mengstr/MCC8/Firmware/MCC8.X/oled.c

#include <stdlib.h>
#include <stdint.h>
#include <string.h>

#include <xc.h>
#include "config.h"
#include "spi.h"
#include "oled.h"


static uint8_t buffer[SSD1306_LCDHEIGHT * SSD1306_LCDWIDTH / 8] = {
0x00, 0x00, 0x00, 0x00, 0x00, 0x00, 0x00, 0x00, 0x00, 0x00, 0x00, 0x00, 0x00, 0x00, 0x00, 0x00,
0x00, 0x00, 0x00, 0x00, 0x00, 0x00, 0x00, 0x00, 0x00, 0x00, 0x00, 0x00, 0x00, 0x00, 0x00, 0x00,
0x00, 0x00, 0x00, 0x00, 0x00, 0x00, 0x00, 0x00, 0x00, 0x00, 0x00, 0x00, 0x00, 0x00, 0x00, 0x00,
0x00, 0x00, 0x00, 0x00, 0x00, 0x00, 0x00, 0x00, 0x00, 0x00, 0x00, 0x00, 0x00, 0x00, 0x00, 0x80,
0x80, 0x80, 0x00, 0x00, 0x00, 0x00, 0x00, 0x00, 0x00, 0x00, 0x00, 0x00, 0x00, 0x00, 0x00, 0x00,
0x00, 0x80, 0x80, 0xC0, 0xC0, 0x00, 0x00, 0x00, 0x00, 0x00, 0x00, 0x00, 0x00, 0x00, 0x00, 0x00,
0x00, 0x00, 0x00, 0x00, 0x00, 0x00, 0x00, 0x00, 0x00, 0x00, 0x00, 0x00, 0x00, 0x00, 0x00, 0x00,
0x00, 0x00, 0x00, 0x00, 0x00, 0x00, 0x00, 0x00, 0x00, 0x00, 0x00, 0x00, 0x00, 0x00, 0x00, 0x00,
0x00, 0x00, 0x00, 0x00, 0x00, 0x00, 0x00, 0x00, 0x00, 0x00, 0x00, 0x00, 0x00, 0x00, 0x00, 0x00,
0x00, 0x00, 0x00, 0x00, 0x80, 0xC0, 0xE0, 0xF0, 0xF8, 0xFC, 0xF8, 0xE0, 0x00, 0x00, 0x00, 0x00,
0x00, 0x00, 0x00, 0x00, 0x00, 0x00, 0x00, 0x00, 0x00, 0x00, 0x00, 0x00, 0x00, 0x80, 0x80, 0x80,
0x80, 0x80, 0x00, 0x80, 0x80, 0x00, 0x00, 0x00, 0x00, 0x80, 0x80, 0x80, 0x80, 0x80, 0x00, 0xFF,
0xFF, 0xFF, 0x00, 0x00, 0x00, 0x00, 0x80, 0x80, 0x80, 0x80, 0x00, 0x00, 0x80, 0x80, 0x00, 0x00,
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
    ,{0x7f, 0x49, 0x49, 0x49, 0x36} // 42 B
    ,{0x3e, 0x41, 0x41, 0x41, 0x22} // 43 C
    ,{0x7f, 0x41, 0x41, 0x22, 0x1c} // 44 D
    ,{0x7f, 0x49, 0x49, 0x49, 0x41} // 45 E
    ,{0x7f, 0x09, 0x09, 0x09, 0x01} // 46 F
    ,{0x3e, 0x41, 0x49, 0x49, 0x7a} // 47 G
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
};



#define SSD1306_CMD_COL_ADD_SET_LSB(column)         (0x00 | (column))
#define SSD1306_CMD_COL_ADD_SET_MSB(column)         (0x10 | (column))
#define SSD1306_CMD_SET_MEMORY_ADDRESSING_MODE      0x20
#define SSD1306_CMD_SET_COLUMN_ADDRESS              0x21
#define SSD1306_CMD_SET_PAGE_ADDRESS                0x22
#define SSD1306_CMD_SET_DISPLAY_START_LINE(line)    (0x40 | (line))
#define SSD1306_CMD_SET_CONTRAST_CONTROL_FOR_BANK0  0x81
#define SSD1306_CMD_SET_CHARGE_PUMP_SETTING         0x8D
#define SSD1306_CMD_SET_SEGMENT_RE_MAP_COL0_SEG0    0xA0
#define SSD1306_CMD_SET_SEGMENT_RE_MAP_COL127_SEG0  0xA1
#define SSD1306_CMD_ENTIRE_DISPLAY_AND_GDDRAM_ON    0xA4
#define SSD1306_CMD_ENTIRE_DISPLAY_ON               0xA5
#define SSD1306_CMD_SET_NORMAL_DISPLAY              0xA6
#define SSD1306_CMD_SET_INVERSE_DISPLAY             0xA7
#define SSD1306_CMD_SET_MULTIPLEX_RATIO             0xA8
#define SSD1306_CMD_SET_DISPLAY_ON                  0xAF
#define SSD1306_CMD_SET_DISPLAY_OFF                 0xAE
#define SSD1306_CMD_SET_PAGE_START_ADDRESS(page)    (0xB0 | (page))
#define SSD1306_CMD_SET_COM_OUTPUT_SCAN_UP          0xC0
#define SSD1306_CMD_SET_COM_OUTPUT_SCAN_DOWN        0xC8
#define SSD1306_CMD_SET_DISPLAY_OFFSET              0xD3
#define SSD1306_CMD_SET_DISPLAY_CLOCK_DIVIDE_RATIO  0xD5
#define SSD1306_CMD_SET_PRE_CHARGE_PERIOD           0xD9
#define SSD1306_CMD_SET_COM_PINS                    0xDA
#define SSD1306_CMD_SET_VCOMH_DESELECT_LEVEL        0xDB
#define SSD1306_CMD_NOP                             0xE3
#define SSD1306_CMD_SCROLL_H_RIGHT                  0x26
#define SSD1306_CMD_SCROLL_H_LEFT                   0x27
#define SSD1306_CMD_CONTINUOUS_SCROLL_V_AND_H_RIGHT 0x29
#define SSD1306_CMD_CONTINUOUS_SCROLL_V_AND_H_LEFT  0x2A
#define SSD1306_CMD_DEACTIVATE_SCROLL               0x2E
#define SSD1306_CMD_ACTIVATE_SCROLL                 0x2F
#define SSD1306_CMD_SET_VERTICAL_SCROLL_AREA        0xA3



//
//
//
void ssd1306_command(uint8_t c) {
    OLED_CS = 1;  // OLED-CS HIGH //digitalWrite(cs, HIGH); *csport |= cspinmask;
    OLED_DC = 0;  // OLED-DC LOW  //digitalWrite(dc, LOW);  *dcport &= ~dcpinmask;
    OLED_CS = 0;  // OLED-CS LOW  //digitalWrite(cs, LOW);  *csport &= ~cspinmask;
    SPI1Write(c);
    OLED_CS = 1;  // OLED-CS HIGH //digitalWrite(cs, HIGH); *csport |= cspinmask;
}


//
//
//
void ssd1306_data(uint8_t c) {
    OLED_CS = 1;  // OLED-CS HIGH //digitalWrite(cs, HIGH); *csport |= cspinmask;
    OLED_DC = 1;  // OLED-DC HIGH  //digitalWrite(dc, LOW);  *dcport &= ~dcpinmask;
    OLED_CS = 0;  // OLED-CS LOW  //digitalWrite(cs, LOW);  *csport &= ~cspinmask;
    SPI1Write(c);
    OLED_CS = 1;  // OLED-CS HIGH //digitalWrite(cs, HIGH); *csport |= cspinmask;
}



uint8_t SSD1306InitSequence[] = {
    0xAE,       // Set display off
    0xD5, 0x80, // Set display clock divide ratio / Osc freqency
    0xA8, 0x3F, // Set multiplex ratio
    0xD3, 0x00, // Set display offset
    0x40,       // Set display start line
    0x8D, 0x14, // Set charge pump (internal)
    0xA0,       // Set display remap
    0xC0,       // Set COM output scan direction
    0xDA, 0x12, // Set COM pins hardware configuraion
    0x81, 0xCF, // Set Contrast (internal)
    0xD9, 0xF1, // Set pre-charge period (internal)
    0xDB, 0x40, // Set DCOMH deselect level
    0x20, 0x00, // Set memery mode
    0xA4,       // Set entire display on/off
    0xA6,       // Set normal/inverse display
    0xAF        // Set display on
};


void OledInit(void) {
    uint8_t i;

    OLED_RES=1;  // VDD (3.3V) goes high at start, lets just chill for a ms
    __delay_ms(10);
    OLED_RES=0;   // bring reset low
    __delay_ms(10);
    OLED_RES=1;   // bring out of reset

    for (i=0; i<sizeof(SSD1306InitSequence); i++) {
        ssd1306_command(SSD1306InitSequence[i]);
    }
}



//
//
//
void OledRefresh(void) {
    uint16_t i;

    ssd1306_command(SSD1306_SETLOWCOLUMN  | 0x0);  // low col = 0
    ssd1306_command(SSD1306_SETHIGHCOLUMN | 0x0);  // hi col = 0
    ssd1306_command(SSD1306_SETSTARTLINE  | 0x0);  // line #0
    ssd1306_command(SSD1306_CMD_SET_PAGE_START_ADDRESS(0));
    ssd1306_command(SSD1306_CMD_COL_ADD_SET_MSB(0 >> 4));
    ssd1306_command(SSD1306_CMD_COL_ADD_SET_LSB(0 & 0x0F));


    OLED_CS = 1;
    OLED_DC = 1;
    OLED_CS = 0;

    for (i=0; i<(SSD1306_LCDWIDTH*SSD1306_LCDHEIGHT/8); i++) {
      SPI1Write(buffer[i]);
    }

    OLED_CS = 1;
}



//
//
//
void OledClear(void) {
  memset(buffer, 0, (SSD1306_LCDWIDTH*SSD1306_LCDHEIGHT/8));
}


static uint8_t xPos;
static uint8_t yPos;

//
//
//
void OledXY(uint8_t _x, uint8_t _y) {
    xPos=_x;
    yPos=_y;
}


void OledPixel(int16_t x, int16_t y, uint16_t color) {
    switch (color) {
        case WHITE:   buffer[x+ (y/8)*SSD1306_LCDWIDTH] |=  (1 << (y&7)); break;
        case BLACK:   buffer[x+ (y/8)*SSD1306_LCDWIDTH] &= ~(1 << (y&7)); break;
        case INVERSE: buffer[x+ (y/8)*SSD1306_LCDWIDTH] ^=  (1 << (y&7)); break;
    }
}


//
//
//
void OledCharacter(char character) {
    uint8_t index;
    uint16_t y;
    y=(yPos/8)*SSD1306_LCDWIDTH;
    buffer[y + xPos++]=0x00;
    for (index= 0; index < 5; index++) {
        buffer[y + xPos++]=ASCII[character - 0x20][index];
    }
}


//
//
//
void OledString(const char *string) {
    while (*string) {
        OledCharacter(*string++);
    }
}
