mengstr/MCC8/Firmware/MCC8.X/games.h

#ifndef GAMES_H_
#define	GAMES_H_

#include <stdint.h>

const uint8_t PUZZLE15[384]={
		0x00,0xe0,0x6c,0x00,0x4c,0x00,0x6e,0x0f,0xa2,0x03,0x60,0x20,0xf0,0x55,0x00,0xe0,0x22,0xbe,0x22,0x76,0x22,0x8e,0x22,0x5e,0x22,0x46,0x12,0x10,0x61,0x00,0x62,0x17,
		0x63,0x04,0x41,0x10,0x00,0xee,0xa2,0xe8,0xf1,0x1e,0xf0,0x65,0x40,0x00,0x12,0x34,0xf0,0x29,0xd2,0x35,0x71,0x01,0x72,0x05,0x64,0x03,0x84,0x12,0x34,0x00,0x12,0x22,
		0x62,0x17,0x73,0x06,0x12,0x22,0x64,0x03,0x84,0xe2,0x65,0x03,0x85,0xd2,0x94,0x50,0x00,0xee,0x44,0x03,0x00,0xee,0x64,0x01,0x84,0xe4,0x22,0xa6,0x12,0x46,0x64,0x03,
		0x84,0xe2,0x65,0x03,0x85,0xd2,0x94,0x50,0x00,0xee,0x44,0x00,0x00,0xee,0x64,0xff,0x84,0xe4,0x22,0xa6,0x12,0x5e,0x64,0x0c,0x84,0xe2,0x65,0x0c,0x85,0xd2,0x94,0x50,
		0x00,0xee,0x44,0x00,0x00,0xee,0x64,0xfc,0x84,0xe4,0x22,0xa6,0x12,0x76,0x64,0x0c,0x84,0xe2,0x65,0x0c,0x85,0xd2,0x94,0x50,0x00,0xee,0x44,0x0c,0x00,0xee,0x64,0x04,
		0x84,0xe4,0x22,0xa6,0x12,0x8e,0xa2,0xe8,0xf4,0x1e,0xf0,0x65,0xa2,0xe8,0xfe,0x1e,0xf0,0x55,0x60,0x00,0xa2,0xe8,0xf4,0x1e,0xf0,0x55,0x8e,0x40,0x00,0xee,0x3c,0x00,
		0x12,0xd2,0x22,0x1c,0x22,0xd8,0x22,0x1c,0xa2,0xf8,0xfd,0x1e,0xf0,0x65,0x8d,0x00,0x00,0xee,0x7c,0xff,0xcd,0x0f,0x00,0xee,0x7d,0x01,0x60,0x0f,0x8d,0x02,0xed,0x9e,
		0x12,0xd8,0xed,0xa1,0x12,0xe2,0x00,0xee,0x01,0x02,0x03,0x04,0x05,0x06,0x07,0x08,0x09,0x0a,0x0b,0x0c,0x0d,0x0e,0x0f,0x00,0x0d,0x00,0x01,0x02,0x04,0x05,0x06,0x08,
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
    {"Tictac",   TICTAC,     sizeof(TICTAC)    },
    {"UFO",      UFO,        sizeof(UFO)       },
    {"Vbrix",    VBRIX,      sizeof(VBRIX)     },
    {"Vers",     VERS,       sizeof(VERS)      },
    {"Wipeoff",  WIPEOFF,    sizeof(WIPEOFF)   }
};



#endif
