mengstr/MCC8/Firmware/MCC8.X/lcd.c

//#include <stdint.h>
//#include <xc.h>
//
//#include "config.h"
//#include "spi.h"
//#include "lcd.h"
//
//
//#ifdef EN_LCD_LOGO
//const uint8_t logo[489] = {
//    0x42, 0xEC, 0x42, 0x03, 0x42, 0xEC, 0x42, 0x03, 0xF8, 0xFE, 0xFE, 0x42, 0xE6, 0x7F, 0x42, 0xE7,
//    0xFE, 0xFC, 0xF0, 0x42, 0x03, 0xF8, 0xFE, 0xFE, 0x42, 0xE6, 0x7F, 0x42, 0xE7, 0xFE, 0xFC, 0xF0,
//    0x00, 0x00, 0xE0, 0xFC, 0xFE, 0xFE, 0x42, 0xE6, 0x7F, 0x42, 0xE6, 0xFE, 0xFE, 0xFC, 0xE0, 0x42,
//    0xED, 0x00, 0x42, 0xED, 0x42, 0x03, 0x42, 0xE9, 0x00, 0x00, 0x42, 0xE9, 0x42, 0x03, 0x42, 0xE9,
//    0x00, 0x00, 0x42, 0xE9, 0x00, 0x00, 0x7F, 0x42, 0xE8, 0x81, 0x00, 0x81, 0x42, 0xE8, 0x7F, 0x42,
//    0xE8, 0x7F, 0x42, 0xE4, 0xC0, 0x42, 0xED, 0x42, 0x03, 0x42, 0xE9, 0x00, 0x00, 0x42, 0x29, 0x42,
//    0x03, 0x42, 0xE9, 0x00, 0x00, 0x42, 0x29, 0x42, 0x03, 0x83, 0xC7, 0xEF, 0x42, 0xED, 0xEF, 0xC7,
//    0x83, 0x00, 0x42, 0xE8, 0x00, 0x42, 0xE9, 0x00, 0x42, 0xE8, 0x42, 0x03, 0x42, 0xE9, 0x00, 0x00,
//    0x42, 0xC9, 0x42, 0x03, 0x42, 0xE9, 0x00, 0x00, 0x42, 0xC9, 0x00, 0x00, 0xFC, 0x42, 0xE8, 0x03,
//    0x01, 0x03, 0x42, 0xE8, 0xFC, 0x42, 0xE8, 0x00, 0x01, 0x42, 0xE7, 0x01, 0x00, 0x42, 0xE8, 0x42,
//    0x03, 0x42, 0xE9, 0xF0, 0xF0, 0x42, 0xE9, 0x42, 0x03, 0x42, 0xE9, 0xF0, 0xF0, 0x42, 0xE9, 0x00,
//    0x00, 0x1F, 0x42, 0xE8, 0xF8, 0xF0, 0xF8, 0x42, 0xE8, 0x1F, 0x42, 0x44, 0x8F, 0x8F, 0x8F, 0x8F,
//    0x00, 0x00, 0x80, 0x8F, 0x0F, 0x8F, 0x8F, 0x0F, 0x00, 0x80, 0x80, 0x0F, 0x0F, 0x8F, 0x8F, 0x8F,
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
//
////    SPIsend(data);
//
//     if (data&0x80) LCD_DI=1; else LCD_DI=0; // D7
//     LCD_CLK=1;  LCD_CLK=0;     // Toggle Clock
//    if (data&0x40) LCD_DI=1; else LCD_DI=0;
//     LCD_CLK=1;  LCD_CLK=0;
//    if (data&0x20) LCD_DI=1; else LCD_DI=0;
//     LCD_CLK=1;  LCD_CLK=0;
//    if (data&0x10) LCD_DI=1; else LCD_DI=0;
//     LCD_CLK=1;  LCD_CLK=0;
//    if (data&0x08) LCD_DI=1; else LCD_DI=0;
//     LCD_CLK=1;  LCD_CLK=0;
//    if (data&0x04) LCD_DI=1; else LCD_DI=0;
//     LCD_CLK=1;  LCD_CLK=0;
//    if (data&0x02) LCD_DI=1; else LCD_DI=0;
//     LCD_CLK=1;  LCD_CLK=0;
//    if (data&0x01) LCD_DI=1; else LCD_DI=0;
//     LCD_CLK=1;  LCD_CLK=0;
//
//     LCD_CE=1;                        // Disable LCD ~CE
//}
//
//
////
////
////
//void LcdInit(void){
//    LCD_LIGHT_TRIS=0;       // Set LCD pins as outputs
//    LCD_CE_TRIS=0;
//    LCD_RESET_TRIS=0;
//  LCD_DI_TRIS=0;
//  LCD_CLK_TRIS=0;
//
//    LcdBacklight(true);
//    LCD_RESET=1;
//    LCD_CE=1;
//  LCD_CLK=0;
//  LCD_DI=0;
//
//    LcdSend(LCD_C, 0xE2);  // Software Reset
//    LcdSend(LCD_C, 0x3D);  // Charge pump ON
//    LcdSend(LCD_C, 0x01);  // Charge pump=4
//    LcdSend(LCD_C, 0xA4);  // Display all points = OFF
//    LcdSend(LCD_C, 0x2F);  // Booster=ON, Voltage Reg=ON, Voltage Follower=ON
//
//    LcdSend(LCD_C, 0xAF);  // Display ON
//
//    //  LcdSend(LCD_C, 0xA7);  // Inverted display
//    LcdSend(LCD_C, 0xA6);  // Normal display
//
//    LcdSend(LCD_C, 0xC0);  // Normal screen up/down
//    //LcdSend(LCD_C, 0xCF);  // Mirror screen up/down
//
//    LcdSend(LCD_C, 0xA0);  // Normal screen left/right
//    //LcdSend(LCD_C, 0xA1);  // Mirror screen left/right
//
////    LcdClear();
//}
//
//
////
////
////
//void LcdXY(uint8_t x, uint8_t y){
//  LcdSend(LCD_C,0xB0 | (y & 0x0F));
//  LcdSend(LCD_C,0x10 | ((x >> 4) & 0x07));
//  LcdSend(LCD_C,0x00 | (x & 0x0F));
//}
//
////
////
////
//void LcdClear(void){
//uint16_t i;
//    for (i=0; i<864 ; i++) {
//        LcdSend(LCD_D, 0x00);
//    }
//}
////
////
////
//void LcdFill(void){
//uint16_t i;
//    for (i=0; i<864 ; i++) {
//        LcdSend(LCD_D, 0xff);
//    }
//}
//
////
////
////
//void LcdCharacter(int8_t character) {
//    int index;
//
//    LcdSend(LCD_D, 0x00);
//    for (index= 0; index < 5; index++) {
//        LcdSend(LCD_D, ASCII[character - 0x20][index]);
//    }
//}
//
////
////
////
//void LcdString(int8_t *characters){
//    while (*characters) {
//        LcdCharacter(*characters++);
//    }
//}
//
//
//
////
////
////
//void LcdBacklight(bool on){
//    LCD_LIGHT=on;
//};
//
//
//
//
//#ifdef EN_LCD_BIGNUM
//void LcdBigNum(uint8_t n, uint8_t x, uint8_t y) {
//    uint8_t *p;
//    uint8_t i;
//
//    LcdXY(96-12-x,1);
//    p=chr12x16;
//    p=p+n*24+23;
//
//    for (i=0; i<12; i++) {
//        LcdSend(LCD_D,*p);
//        p-=2;
//    }
//    p+=23;
//    LcdXY(96-12-x,0);
//    for (i=0; i<12; i++) {
//        LcdSend(LCD_D,*p);
//        p-=2;
//    }
//
//}
//#endif
//
//
//#ifdef EN_LCD_HUGENUM
//void LcdHugeNum(uint8_t n, uint8_t x, uint8_t y) {
//    uint8_t *p;
//    uint8_t i;
//
//    p=chr24x32+n*96;
//
//    LcdXY(x,0+y);
//    for (i=0; i<24; i++) {
//        LcdSend(LCD_D,*p);
//        p+=4;
//    }
//
//    p-=95;
//    LcdXY(x,1+y);
//    for (i=0; i<24; i++) {
//        LcdSend(LCD_D,*p);
//        p+=4;
//    }
//
//    p-=95;
//    LcdXY(x,2+y);
//    for (i=0; i<24; i++) {
//        LcdSend(LCD_D,*p);
//        p+=4;
//    }
//
//    p-=95;
//    LcdXY(x,3+y);
//    for (i=0; i<24; i++) {
//        LcdSend(LCD_D,*p);
//        p+=4;
//    }
//}
//#endif
//
//
//#ifdef EN_LCD_LOGO
////
////
////
//void LcdLogo(void) {
//    uint16_t i,j;
//    LcdXY(0,0);
//    for (i=0; i<sizeof(logo); i++) {
//        if (logo[i]==0x42) {
//            i++;
//            if (logo[i]==0x42) {
//                LcdSend(LCD_D, logo[i]);
//            } else {
//                for (j=0; j<(logo[i]&0x1F); j++) {
//                    if ((logo[i]&0xE0)==0x00) LcdSend(LCD_D, 0x00); //Code 0x00
//                    if ((logo[i]&0xE0)==0x20) LcdSend(LCD_D, 0x07); //Code 0x20
//                    if ((logo[i]&0xE0)==0x40) LcdSend(LCD_D, 0x0F); //Code 0x40
//                    if ((logo[i]&0xE0)==0x60) LcdSend(LCD_D, 0x08); //Code 0x60
//                    if ((logo[i]&0xE0)==0x80) LcdSend(LCD_D, 0x40); //Code 0x80
//                                                                    //Code 0xA0
//                    if ((logo[i]&0xE0)==0xC0) LcdSend(LCD_D, 0xFE); //Code 0xC0
//                    if ((logo[i]&0xE0)==0xE0) LcdSend(LCD_D, 0xFF); //Code 0xE0
//                }
//            }
//
//        } else {
//            LcdSend(LCD_D, logo[i]);
//        }
//    }
//}
//#endif
//
//#endif
